madworm/Pentax-S5z-LED-ring/gerber_files/PNGs/Pentax-S5z-LED-ring-F_SilkS.gto.png

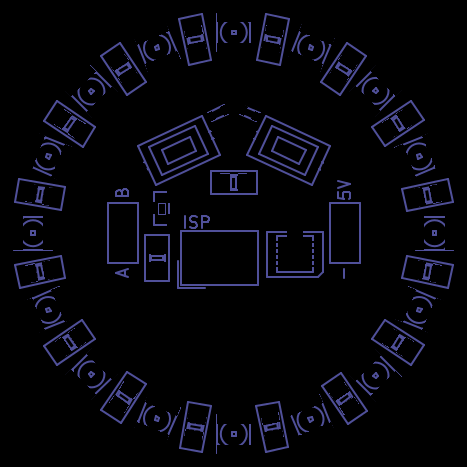
gerber_files/PNGs/Pentax-S5z-LED-ring-F_SilkS.gto.png
