madworm/Pentax-S5z-LED-ring/gerber_files/PNGs/Pentax-S5z-LED-ring.drl.png

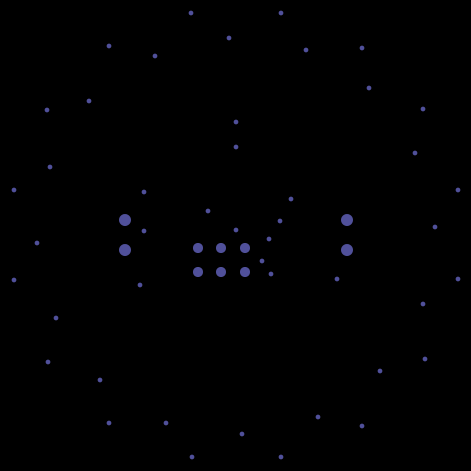
gerber_files/PNGs/Pentax-S5z-LED-ring.drl.png
