madworm/Pentax-S5z-LED-ring/gerber_files/PNGs/Pentax-S5z-LED-ring__back_purple.png

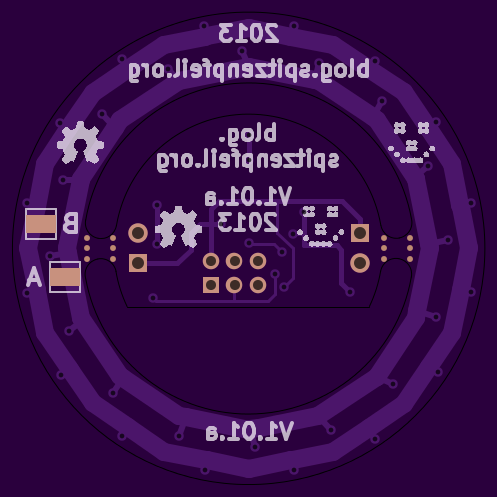
gerber_files/PNGs/Pentax-S5z-LED-ring__back_purple.png
